zephray/VerilogBoy/hardware/3d_models/PJ-313D.SLDPRT

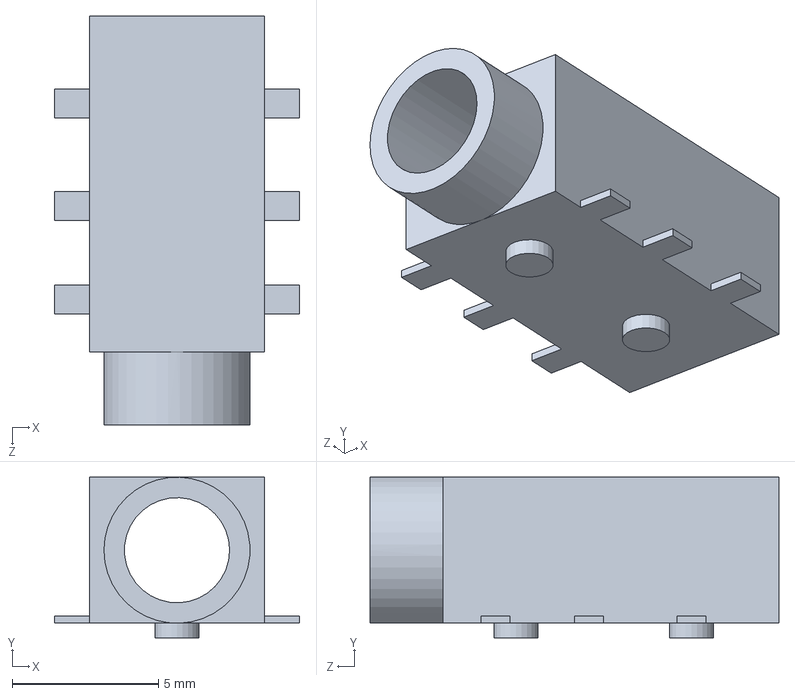
[picture p16: CAD file, 2018-10-20, last stored version]
hardware/3d_models/PJ-313D.SLDPRT
8.40 x 5.50 x 14.0 mm
