zephray/VerilogBoy/hardware/3d_models/bl_5c.SLDPRT

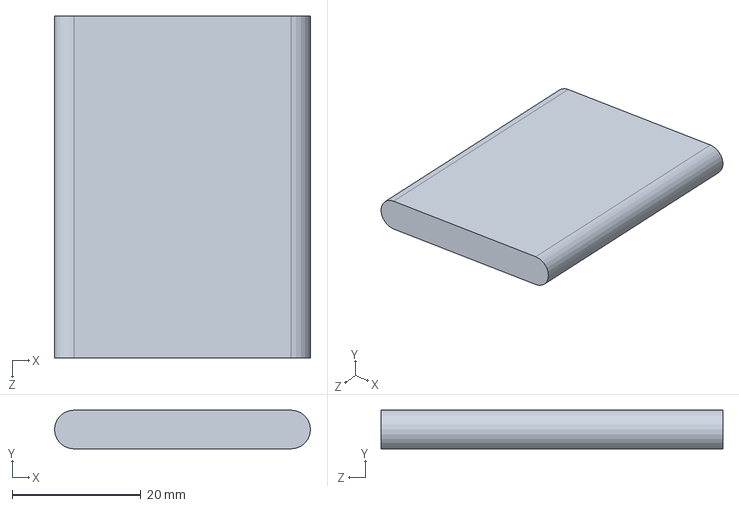
[picture p17: CAD file, 2018-10-15, last stored version]
hardware/3d_models/bl_5c.SLDPRT
39.7 x 6.00 x 53.0 mm
