zephray/VerilogBoy/hardware/3d_models/bp_6m.SLDPRT

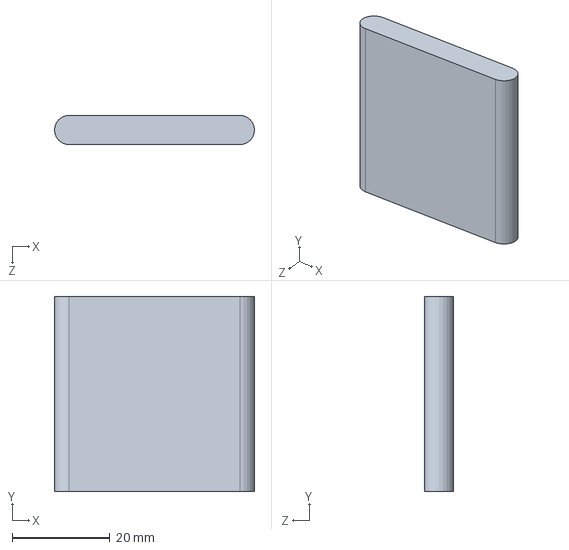
[picture p18: CAD file, 2018-10-15, last stored version]
hardware/3d_models/bp_6m.SLDPRT
41.0 x 40.0 x 6.00 mm
