zephray/VerilogBoy/hardware/3d_models/dpad.SLDPRT

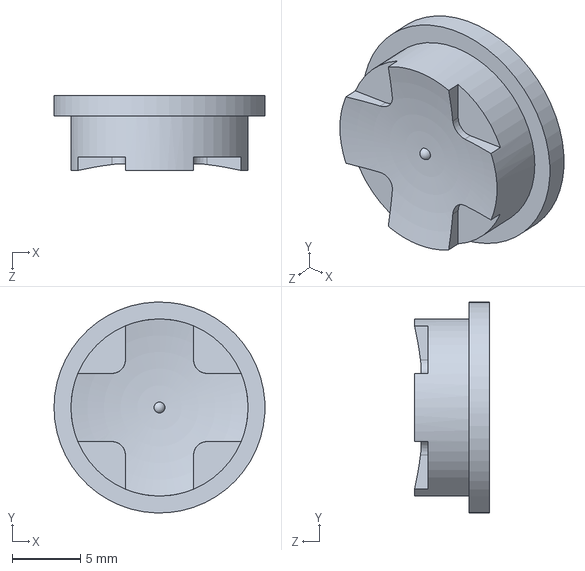
[picture p19: CAD file, 2018-10-15, last stored version]
hardware/3d_models/dpad.SLDPRT
15.5 x 15.5 x 5.50 mm
